AlanFromJapan/Homebrew-Gameboy-Cartridge/board alan v1.0.png

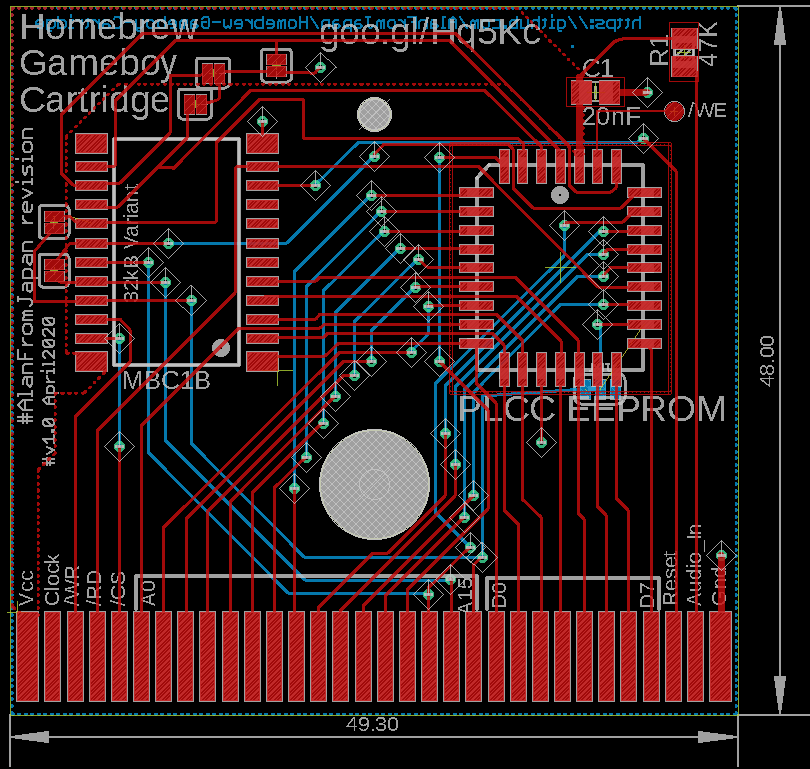
board alan v1.0.png
